navan93/BLE-Sensor-Board/FW/nrf52805-adv/hw/bsp/nrf52805/src/hal_bsp.c

#include <stdint.h>
#include <stddef.h>
#include <assert.h>
#include "os/mynewt.h"
#include "mynewt_cm.h"
#include "nrfx.h"
#include "flash_map/flash_map.h"
#include "hal/hal_bsp.h"
#include "hal/hal_flash.h"
#include "hal/hal_system.h"
#include "mcu/nrf52_hal.h"
#include "mcu/nrf52_periph.h"
#include "bsp/bsp.h"
#include "defs/sections.h"

/** What memory to include in coredump. */
static const struct hal_bsp_mem_dump dump_cfg[] = {
    [0] = {
        .hbmd_start = &_ram_start,
        .hbmd_size = RAM_SIZE,
    }
};

const struct hal_bsp_mem_dump *
hal_bsp_core_dump(int *area_cnt)
{
    *area_cnt = sizeof(dump_cfg) / sizeof(dump_cfg[0]);
    return dump_cfg;
}

int
hal_bsp_power_state(int state)
{
    return (0);
}
/**
 * Retrieves the flash device with the specified ID.  Returns NULL if no such
 * device exists.
 */
const struct hal_flash *
hal_bsp_flash_dev(uint8_t id)
{
    switch (id) {
    case 0:
        /* MCU internal flash. */
        return &nrf52k_flash_dev;

    default:
        /* External flash.  Assume not present in this BSP. */
        return NULL;
    }
}

/**
 * Retrieves the configured priority for the given interrupt. If no priority
 * is configured, returns the priority passed in.
 *
 * @param irq_num               The IRQ being queried.
 * @param pri                   The default priority if none is configured.
 *
 * @return uint32_t             The specified IRQ's priority.
 */
uint32_t
hal_bsp_get_nvic_priority(int irq_num, uint32_t pri)
{
    uint32_t cfg_pri;

    switch (irq_num) {
    /* Radio gets highest priority */
    case RADIO_IRQn:
        cfg_pri = 0;
        break;
    default:
        cfg_pri = pri;
    }
    return cfg_pri;
}

void
hal_bsp_init(void)
{
    int rc;

    (void)rc;

    /* Make sure system clocks have started. */
    hal_system_clock_start();

    /* Initialize additional BSP peripherals here. */
    nrf52_periph_create();
}

void
hal_bsp_deinit(void)
{
    Cortex_DisableAll();
}
